Diwamoto/sage60/mechanical/gasket_v1/sage60_left_case_contour_top.stl

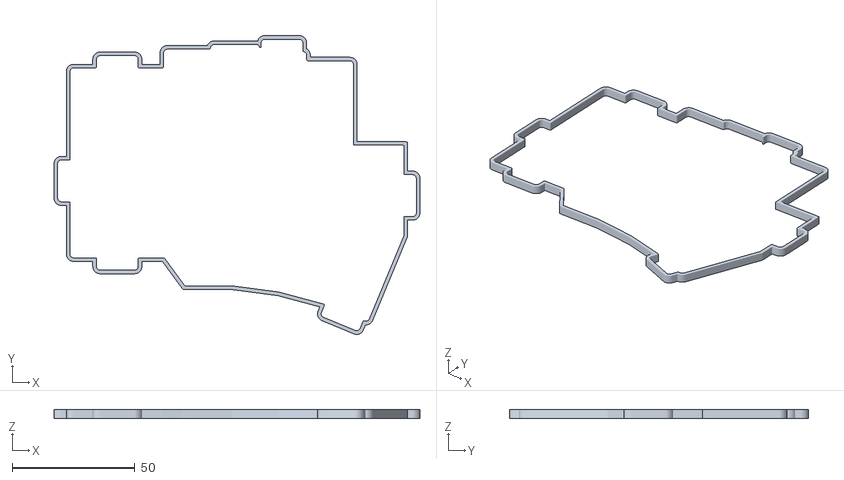
[picture p17: CAD file, 2026-09-17]
mechanical/gasket_v1/sage60_left_case_contour_top.stl
148.8 x 121.5 x 3.50
