Diwamoto/sage60/mechanical/gasket_v1/sage60_right_tb_case_bottom.step

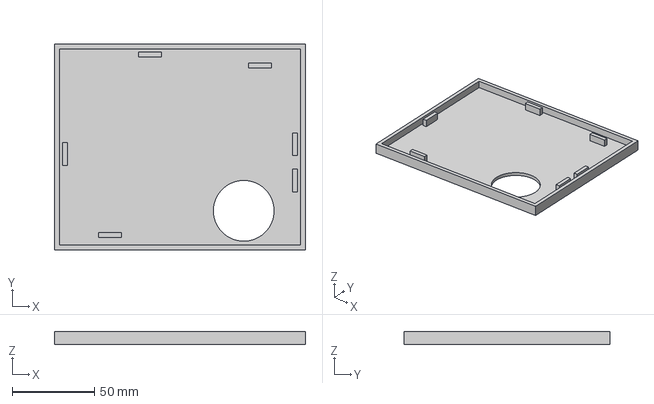
[picture p18: CAD file, 2026-09-17]
mechanical/gasket_v1/sage60_right_tb_case_bottom.step
152.9 x 125.6 x 8.00 mm
