Diwamoto/sage60/mechanical/gasket_v1/sage60_right_tb_case_v3_top.stl

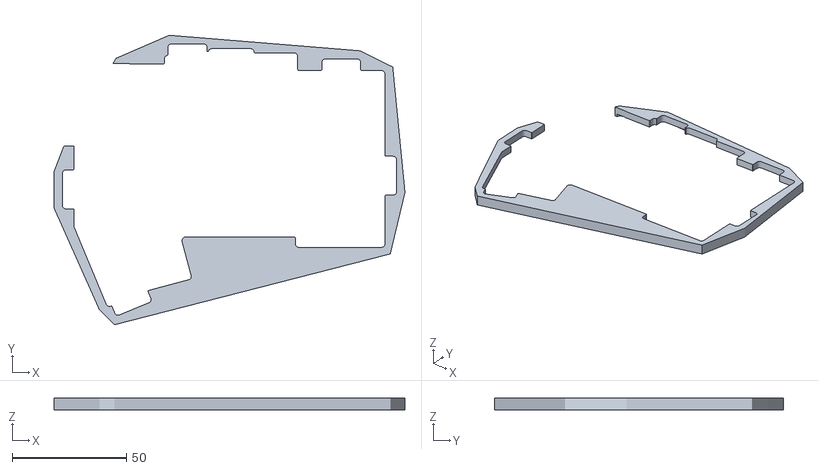
[picture p19: CAD file, 2026-09-17]
mechanical/gasket_v1/sage60_right_tb_case_v3_top.stl
153.3 x 126.4 x 5.20
