Diwamoto/sage60/mechanical/gasket_v1/sage60_right_tb_case_v3_bottom.step

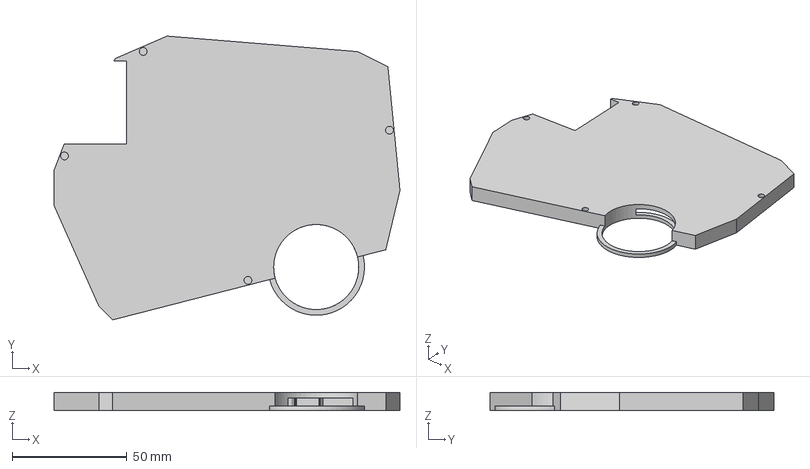
[picture p20: CAD file, 2026-09-17]
mechanical/gasket_v1/sage60_right_tb_case_v3_bottom.step
150.5 x 123.4 x 8.00 mm
