Diwamoto/sage60/mechanical/gasket_v1/sage60_right_tb_case_contour_top.stl

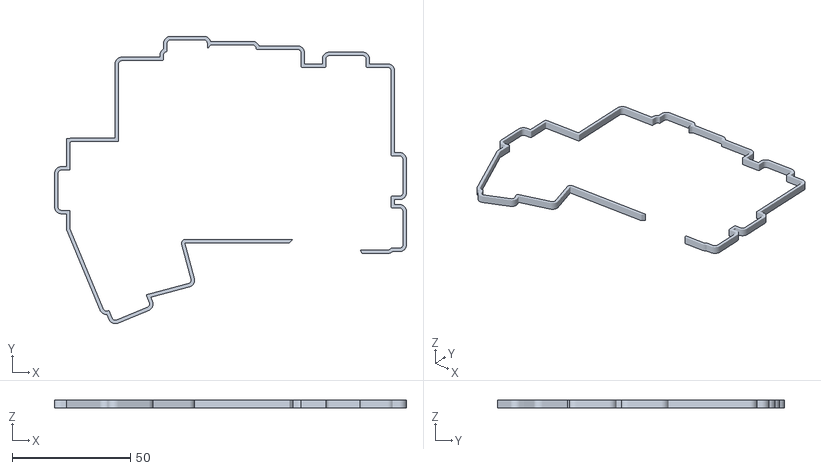
[picture p21: CAD file, 2026-09-17]
mechanical/gasket_v1/sage60_right_tb_case_contour_top.stl
148.8 x 121.5 x 3.50
